temporaerhaus/ttn-ulm-pcb/pcb/img/raw_files/ttn.png

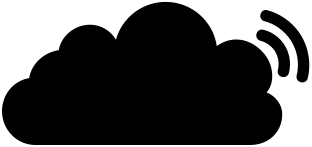
pcb/img/raw_files/ttn.png
