temporaerhaus/ttn-ulm-pcb/pcb/img/screenshots/PCB-Screenshot.png

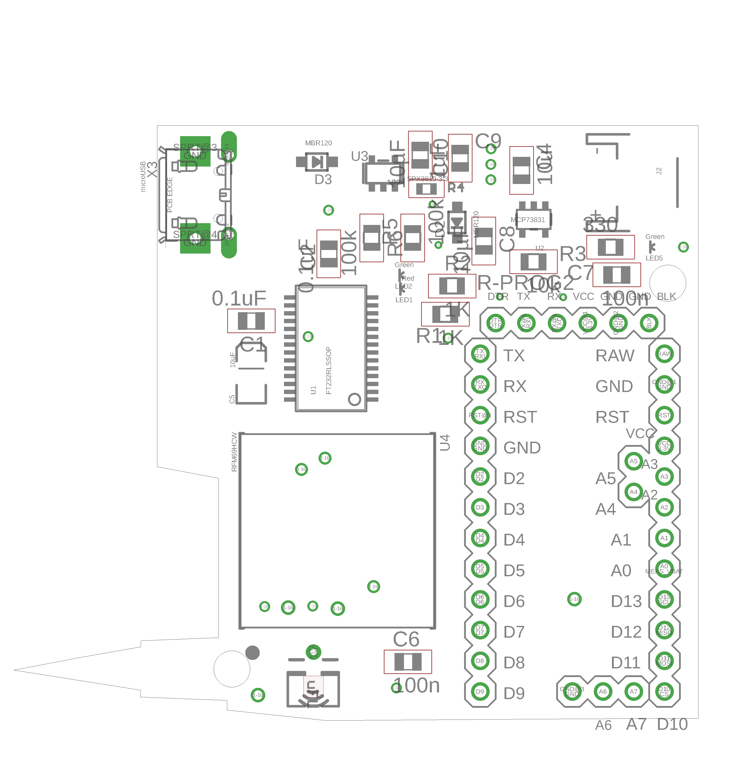
pcb/img/screenshots/PCB-Screenshot.png
