temporaerhaus/ttn-ulm-pcb/pcb/panelized/minster_Combined_Bottom.png

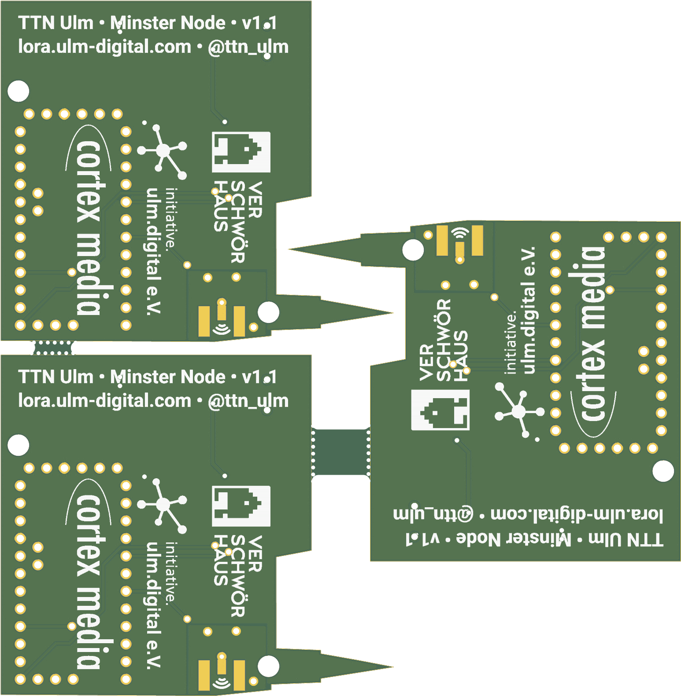
pcb/panelized/minster_Combined_Bottom.png
