temporaerhaus/ttn-ulm-pcb/pcb/panelized/minster_Combined_Top.png

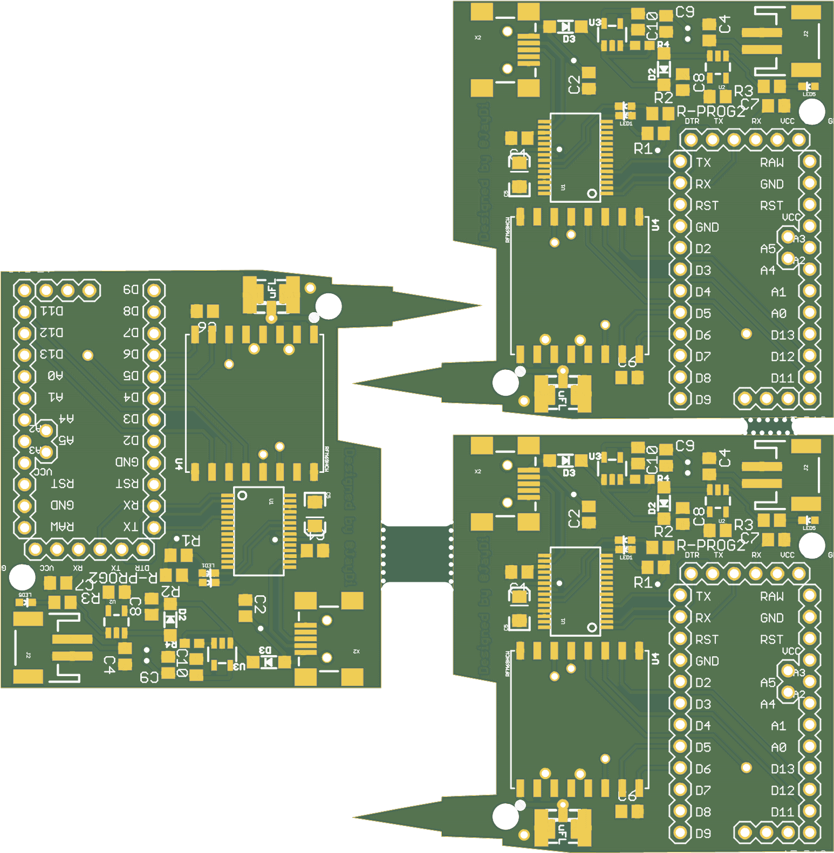
pcb/panelized/minster_Combined_Top.png
